djgreeb/Sampler-DJS-500/Screenshots/SCREEN_795.bmp

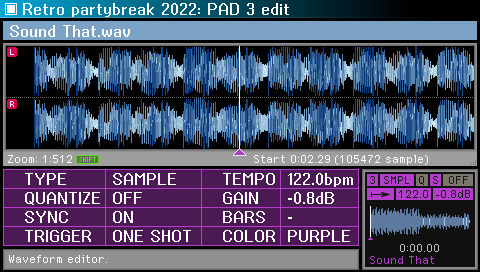
Screenshots/SCREEN_795.bmp
