djgreeb/Sampler-DJS-500/CNC FILES/Button PCB/board.jpg

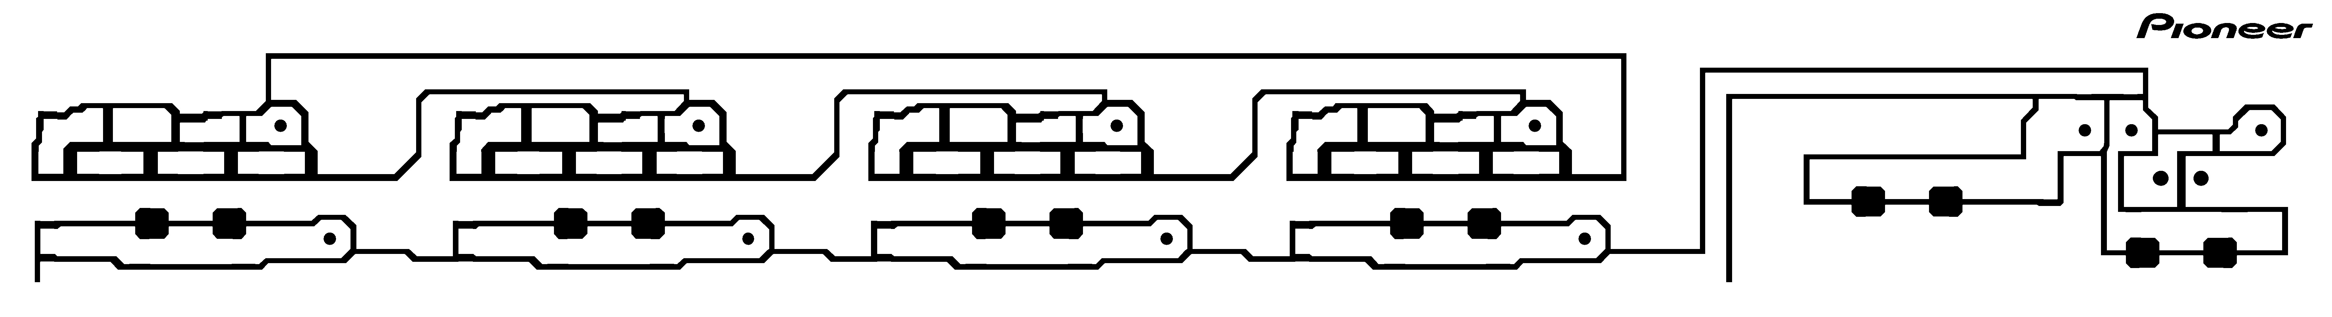
CNC FILES/Button PCB/board.jpg
