djgreeb/Sampler-DJS-500/CNC FILES/Encoder Board/board.jpg

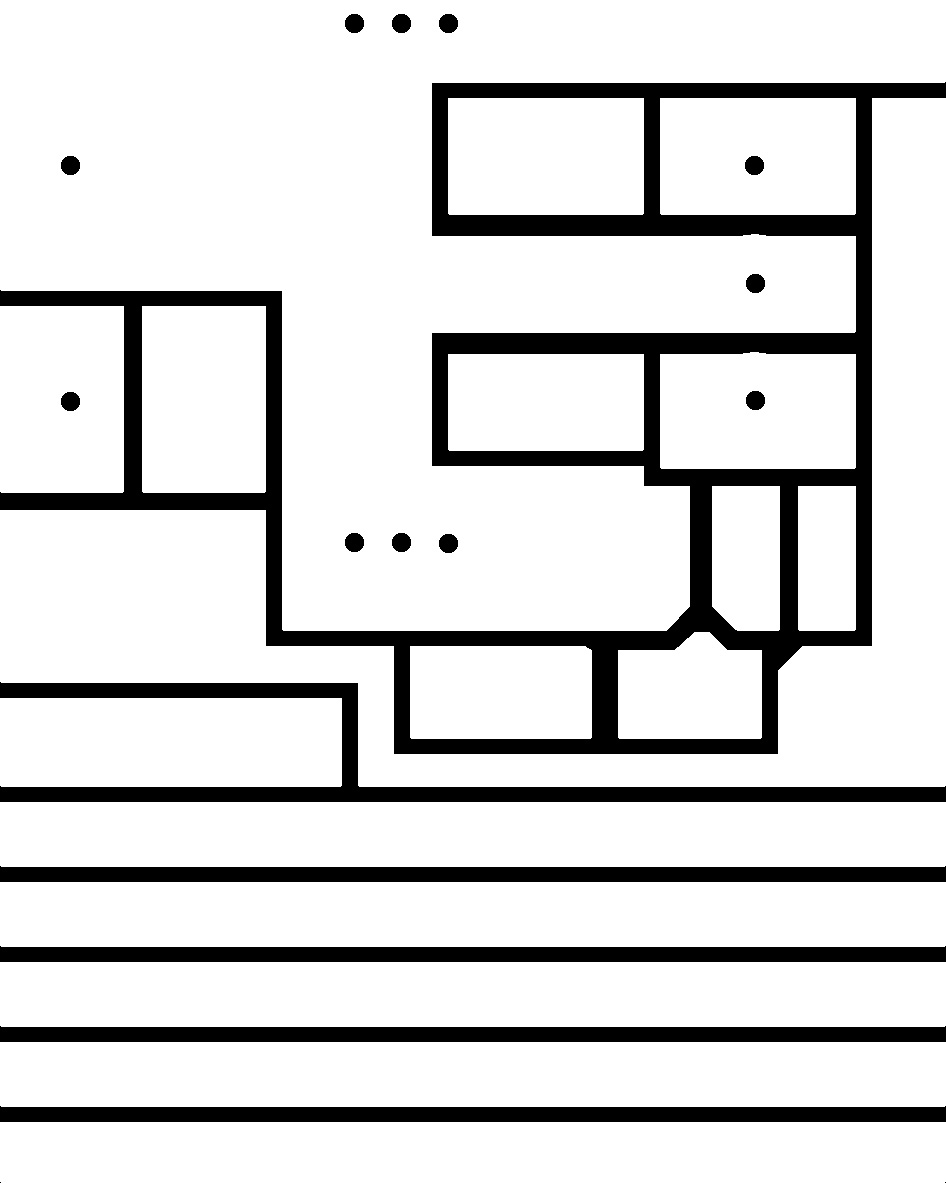
CNC FILES/Encoder Board/board.jpg
