djgreeb/Sampler-DJS-500/Screenshots/SCREEN_009.bmp

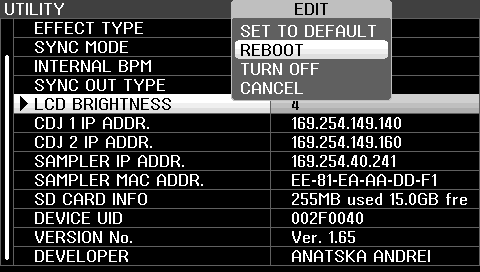
Screenshots/SCREEN_009.bmp
