djgreeb/Sampler-DJS-500/Screenshots/SCREEN_110.bmp

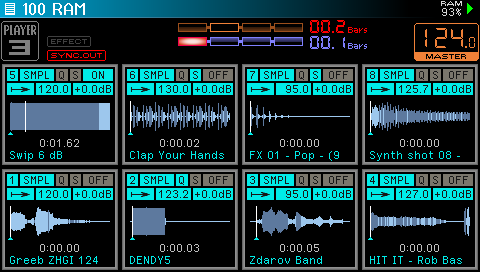
Screenshots/SCREEN_110.bmp
