djgreeb/Sampler-DJS-500/Screenshots/SCREEN_176.bmp

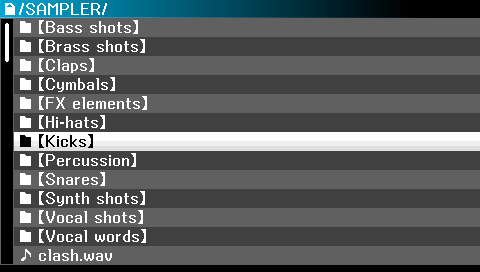
Screenshots/SCREEN_176.bmp
