djgreeb/Sampler-DJS-500/Screenshots/SCREEN_189.bmp

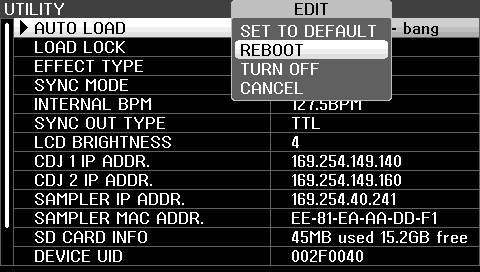
Screenshots/SCREEN_189.bmp
