djgreeb/Sampler-DJS-500/Screenshots/SCREEN_191.bmp

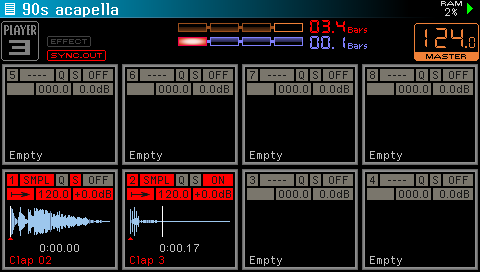
Screenshots/SCREEN_191.bmp
