djgreeb/Sampler-DJS-500/Screenshots/SCREEN_217 new.bmp

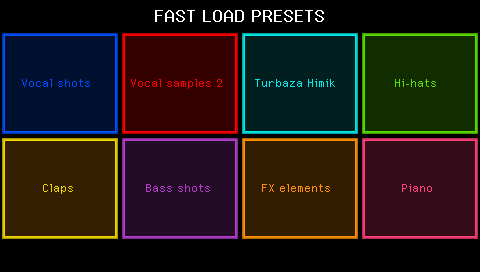
Screenshots/SCREEN_217 new.bmp
