djgreeb/Sampler-DJS-500/Screenshots/SCREEN_217.bmp

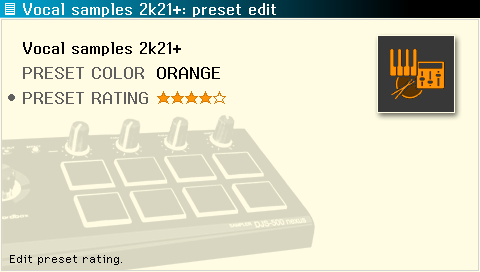
Screenshots/SCREEN_217.bmp
