djgreeb/Sampler-DJS-500/Screenshots/SCREEN_236.bmp

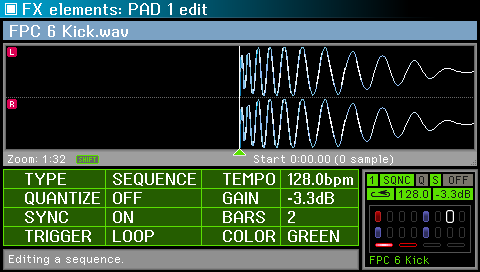
Screenshots/SCREEN_236.bmp
