djgreeb/Sampler-DJS-500/Screenshots/SCREEN_249.bmp

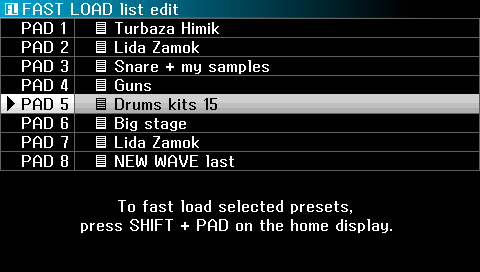
Screenshots/SCREEN_249.bmp
