djgreeb/Sampler-DJS-500/Screenshots/SCREEN_285.bmp

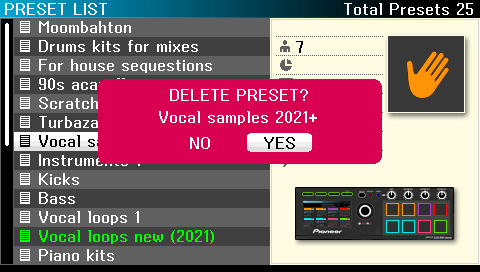
Screenshots/SCREEN_285.bmp
