djgreeb/Sampler-DJS-500/Screenshots/SCREEN_449_new.bmp

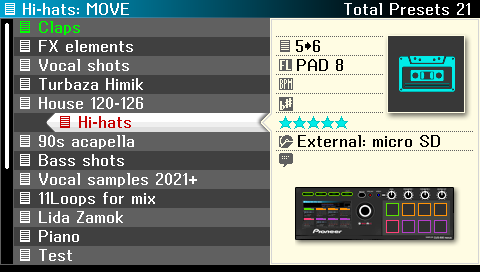
Screenshots/SCREEN_449_new.bmp
