djgreeb/Sampler-DJS-500/Screenshots/SCREEN_734.bmp

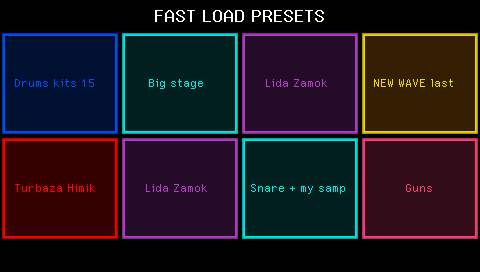
Screenshots/SCREEN_734.bmp
