djgreeb/Sampler-DJS-500/Screenshots/SCREEN_740.bmp

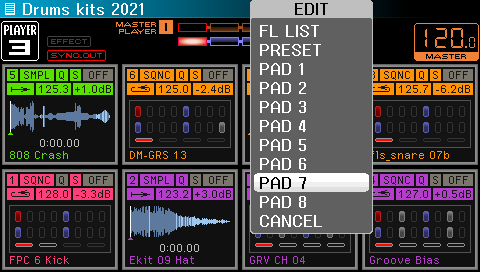
Screenshots/SCREEN_740.bmp
