djgreeb/Sampler-DJS-500/Screenshots/SCREEN_757.bmp

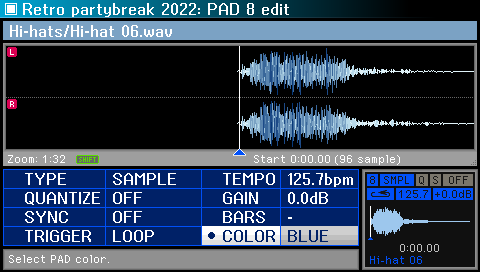
Screenshots/SCREEN_757.bmp
