djgreeb/Sampler-DJS-500/Screenshots/SCREEN_758.bmp

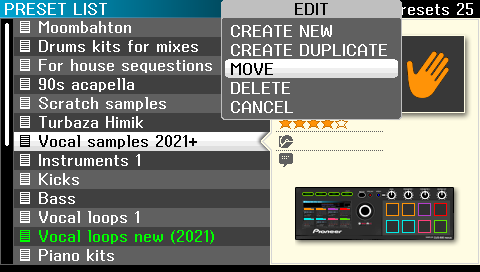
Screenshots/SCREEN_758.bmp
