djgreeb/Sampler-DJS-500/Screenshots/SCREEN_829.bmp

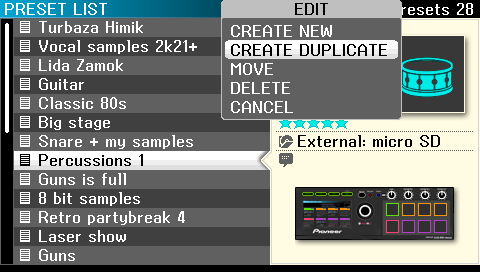
Screenshots/SCREEN_829.bmp
