djgreeb/Sampler-DJS-500/Screenshots/SCREEN_905_new.bmp

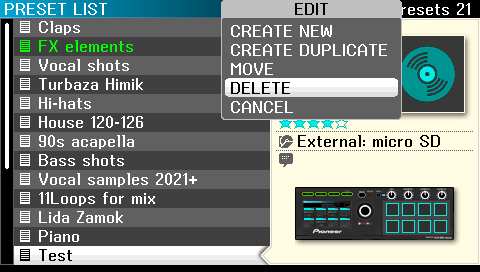
Screenshots/SCREEN_905_new.bmp
