djgreeb/Sampler-DJS-500/Screenshots/SCREEN_956.bmp

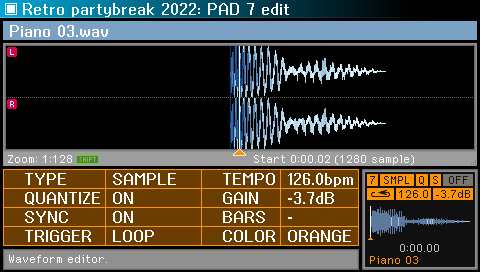
Screenshots/SCREEN_956.bmp
