djgreeb/Sampler-DJS-500/Firmware/Sampler/Inc/audio.h

/////////////////////////////////////////////////////////////////////////////////////////////////
// Audio processing variables
//	product: DJS-500 sampler
//
//
//
//
//	Author: Anatska Andrei
//
/////////////////////////////////////////////////////////////////////////////////////////////////

#include "stdint.h"

uint16_t PCM_2[2];
int16_t LR[2][4];
float c0, c1, c2, c3, r0, r1, r2, r3;
int32_t even1, even2, odd1, odd2;
uint32_t all_long = 0;						//Long sample in samples (44100 per second)
uint32_t play_adr = 0;						//Playing adress in samples (44100 per second)
uint32_t sdram_adr = 0;
uint8_t SAMPLE[4];
uint16_t PCM[206][8192][2]					__attribute__ ((section(".sdram")));;
uint16_t sai_pitch = 0;	// 10000 = 100% step 0,01%
uint16_t pitch = 0;	// 10000 = 100% step 0,01%	
uint32_t tmp_pitch;
uint32_t position = 0;
uint8_t step_position = 0;
float SAMPLE_0, SAMPLE_1;
float T;
uint8_t	end_of_track = 0;			//end track flag
uint16_t TIM_DIVIDER = 0; 
uint8_t TIM_LED_DIV = 0;
uint32_t music_tim = 0xFFFFFFFF;			//timer for bpm tick in ms
uint32_t SQN[3] = {0xFFFFFFFF, 0xFFFFFFFF, 0xFFFFFFFF};
uint32_t SMPL_STRT = 0;
uint32_t SHFT_STRT = 0;				//shift start for quantize
uint8_t force_start_sample = 0;		//force start for quantize starting
uint8_t BEAT_CNT = 0;   //0...15 max
uint8_t PARTBEAT_CNT = 0;   //0...3 max
uint8_t end_one_shot_seq = 0;
uint8_t ATT_LVL = 0xFF;

const static float COEF[8] = {			//////optimal 2x
									0.45868970870461956,
									0.04131401926395584,
									0.48068024766578432,
									0.17577925564495955,
									-0.246185007019907091, 
									0.24614027139700284,
									-0.36030925263849456,
									0.10174985775982505
									};

									
const static float ATNTR[256] = {
0.90000,
0.88969,
0.87951,
0.86944,
0.85949,
0.84965,
0.83992,
0.83031,
0.82080,
0.81141,
0.80212,
0.79294,
0.78386,
0.77489,
0.76602,
0.75725,
0.74858,
0.74001,
0.73154,
0.72317,
0.71489,
0.70671,
0.69862,
0.69062,
0.68271,
0.67490,
0.66717,
0.65954,
0.65199,
0.64452,
0.63715,
0.62985,
0.62264,
0.61552,
0.60847,
0.60150,
0.59462,
0.58781,
0.58108,
0.57443,
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
};





/* Effects variables ---------------------------------------------------------*/
uint8_t dk;
uint8_t trans_mute = 0;
uint8_t previous_trans_mute = 0;
uint8_t inv_VR_LEVEL;
uint32_t vlevel_mux;
uint32_t mbp_mux;
uint8_t fade = 0;



const static float ATT[24] = 
{
0.0000,
0.0434,
0.0869,
0.1304,
0.1739,
0.2173,
0.2608,
0.3043,
0.3478,
0.3913,
0.4347,
0.4782,
0.5217,
0.5652,
0.6086,
0.6521,
0.6956,
0.7391,
0.7826,
0.8260,
0.8695,
0.9130,
0.9565,
1.0000
};


const static float VR_POS[128] = {
0.00001,
0.00787,
0.01574,
0.02362,
0.03149,
0.03937,
0.04724,
0.05511,
0.06299,
0.07086,
0.07874,
0.08661,
0.09448,
0.10236,
0.11023,
0.11811,
0.12598,
0.13385,
0.14173,
0.14960,
0.15748,
0.16535,
0.17322,
0.18110,
0.18897,
0.19685,
0.20472,
0.21259,
0.22047,
0.22834,
0.23622,
0.24409,
0.25196,
0.25984,
0.26771,
0.27559,
0.28346,
0.29133,
0.29921,
0.30708,
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


float SM0, SM1;


//////////////////////////////Moog filter
float in1, in2, in3, in4, out1, out2, out3, out4;
float fcutoff, resonanse;





////////////////////////////////////////////////////////////////////////////////////////////////////////////////////////
